lfantoniosi/WonderTANG/images/WonderTANG-V1.0-back-render.png

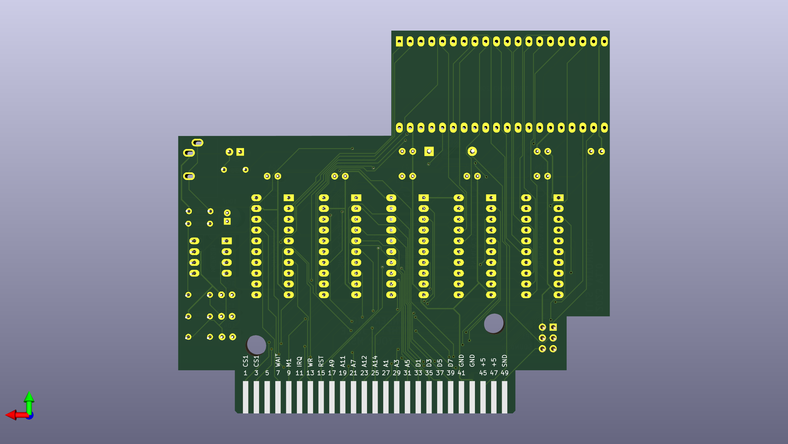
images/WonderTANG-V1.0-back-render.png
