lfantoniosi/WonderTANG/images/WonderTANG-V1.0-front-render.png

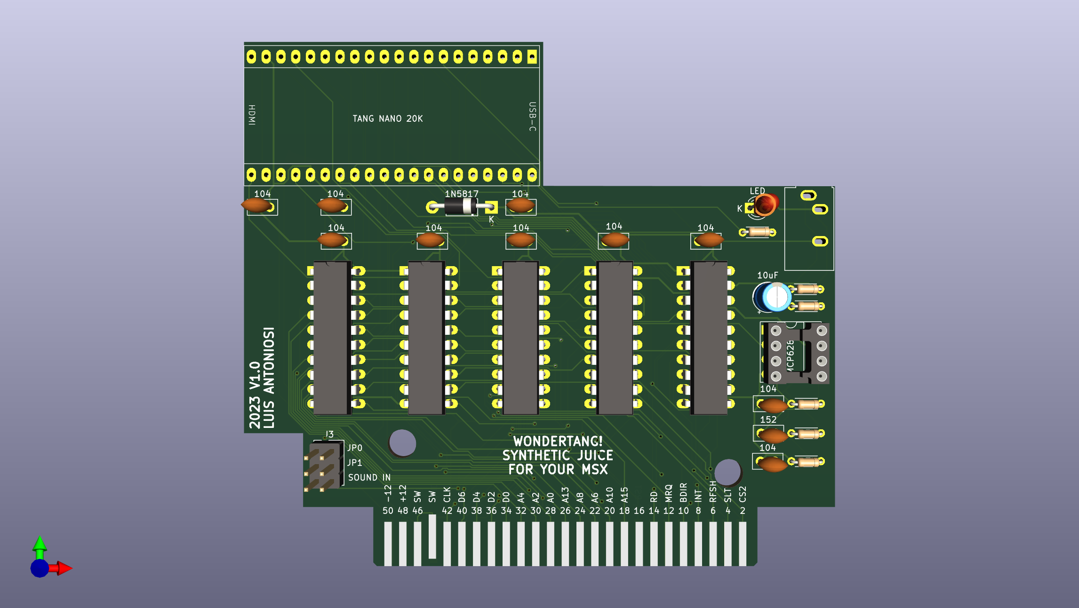
images/WonderTANG-V1.0-front-render.png
