lfantoniosi/WonderTANG/fpga/src/pinfilter.v

// filter noise from GPIO pins
// takes 2 cycles with enabled signal to stabilize a line

module pinfilter
(
    input clk,
    input reset_n,
    input din,
    input ena,
    output dout
);

    reg [1:0] dpipe;
    reg latch;
    wire o;

    always @(posedge clk or negedge reset_n) begin
    if (~reset_n) begin
            dpipe <= 2'b11;
        end else begin
            if (ena) begin
                dpipe <= { dpipe[0], din };
                latch <= o;      
            end
        end
    end

    assign o = (dpipe[1:0] == 2'b00) ? 1'b0 : (dpipe[1:0] == 2'b11) ? 1'b1 : latch;

    assign dout = o;

endmodule

module pinfilter_reg
(
    input clk,
    input reg_clk,
    input reset_n,
    input din,
    input ena,
    output dout
);

    reg [1:0] dpipe;
    reg d, latch;
    wire o;

    always @(posedge clk or negedge reset_n) begin
    if (~reset_n) begin
            dpipe <= 2'b11;
            d <= 2'b1;
        end else begin
            if (ena) begin
                dpipe <= { dpipe[0], din };
                d <= (dpipe[1:0] == 2'b00) ? 1'b0 : (dpipe[1:0] == 2'b11) ? 1'b1 : d; 
                latch <= o;     
            end
        end
    end

    assign o = (reg_clk) ? d : latch;

    assign dout = o;

endmodule
