lfantoniosi/WonderTANG/fpga/src/gowin_rpll/clkp54_tmp.v

//Copyright (C)2014-2023 Gowin Semiconductor Corporation.
//All rights reserved.
//File Title: Template file for instantiation
//GOWIN Version: V1.9.9 Beta-4 Education
//Part Number: GW2AR-LV18QN88C8/I7
//Device: GW2AR-18
//Device Version: C
//Created Time: Sun Jun  9 16:23:21 2024

//Change the instance name and port connections to the signal names
//--------Copy here to design--------

    clkpk54 your_instance_name(
        .clkout(clkout_o), //output clkout
        .lock(lock_o), //output lock
        .clkoutp(clkoutp_o), //output clkoutp
        .clkoutd(clkoutd_o), //output clkoutd
        .reset(reset_i), //input reset
        .clkin(clkin_i) //input clkin
    );

//--------Copy end-------------------
